fuanxka/SlimeVR-Tracker/参考文件/效果图/SlimeVR-Tracker-3D打印预览-1.png

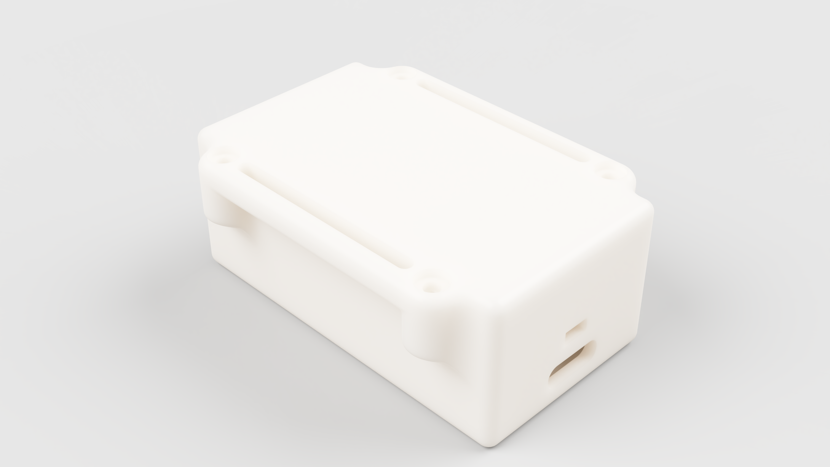
参考文件/效果图/SlimeVR-Tracker-3D打印预览-1.png
