fuanxka/SlimeVR-Tracker/参考文件/效果图/SlimeVR-Tracker-PCB预览2.png

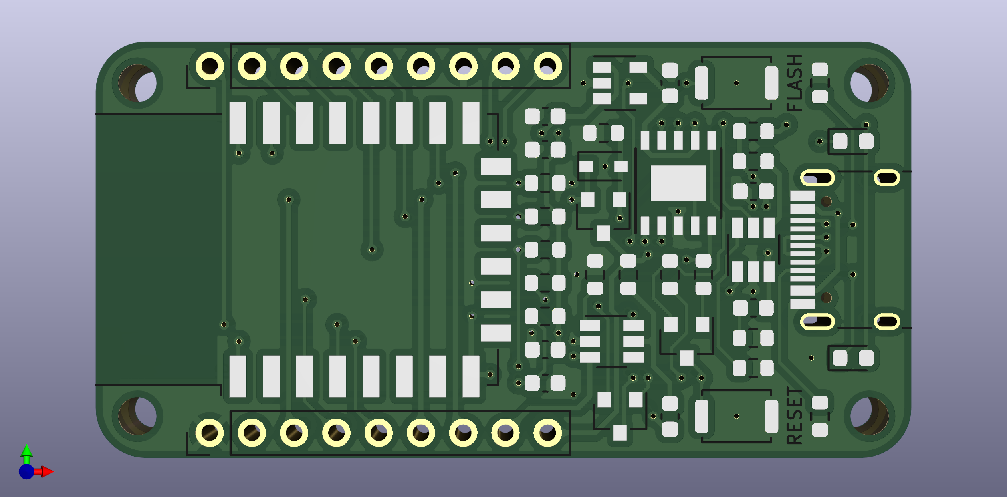
参考文件/效果图/SlimeVR-Tracker-PCB预览2.png
