fuanxka/SlimeVR-Tracker/参考文件/效果图/SlimeVR-Tracker-SMT-3D打印预览.png

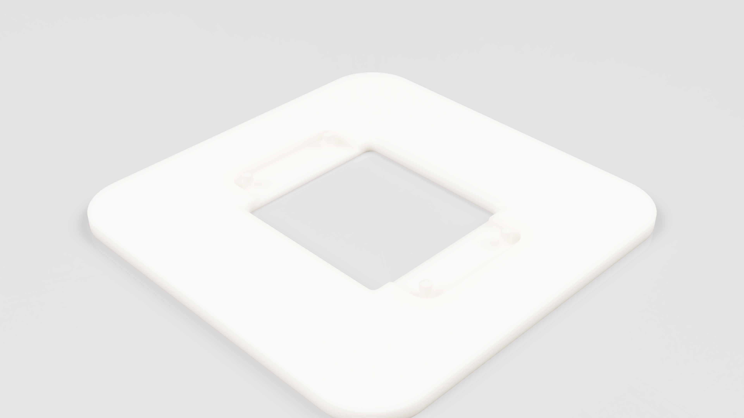
参考文件/效果图/SlimeVR-Tracker-SMT-3D打印预览.png
