fuanxka/SlimeVR-Tracker/参考文件/效果图/SlimeVR-Tracker-成品充电效果（充满）.jpg

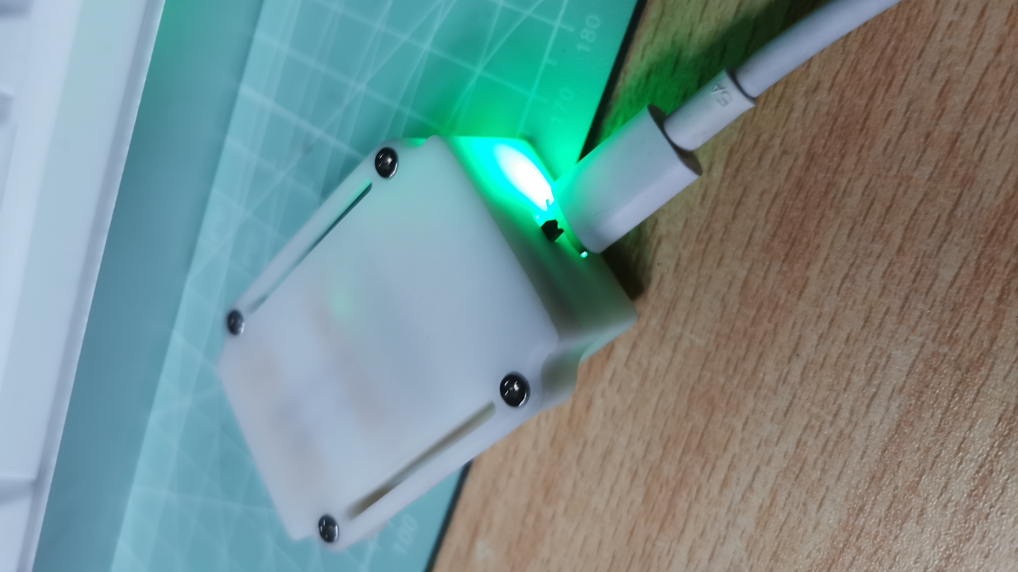
参考文件/效果图/SlimeVR-Tracker-成品充电效果（充满）.jpg
